emilianmanoleuni/ESP-DOMOTIC-SYSTEM/esp_main/esp_main_data/data/background.jpg

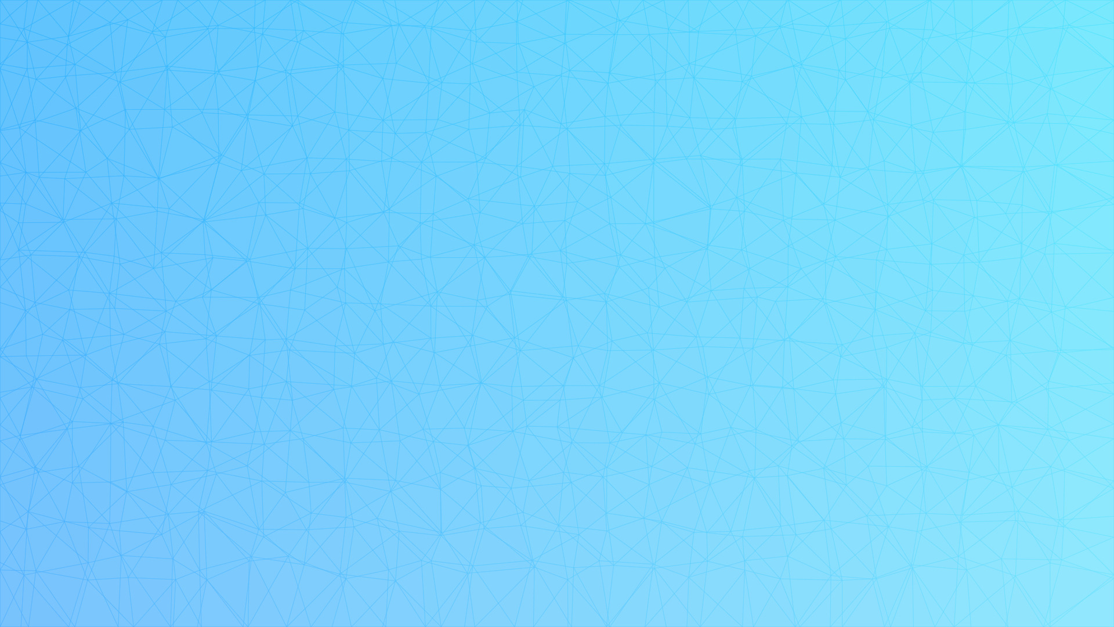
esp_main/esp_main_data/data/background.jpg
