emilianmanoleuni/ESP-DOMOTIC-SYSTEM/esp_main/esp_main_data/data/casa_grafica.png

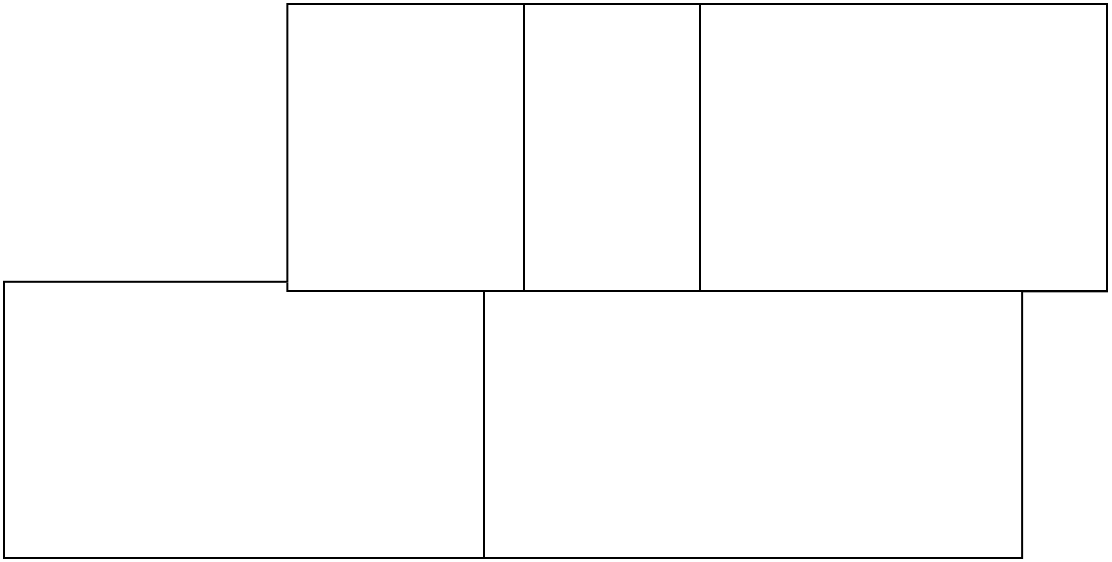
esp_main/esp_main_data/data/casa_grafica.png
